vaeyias/one-handed-game-controller/2024_fall/Showcase/FINALHANDLE.SLDPRT

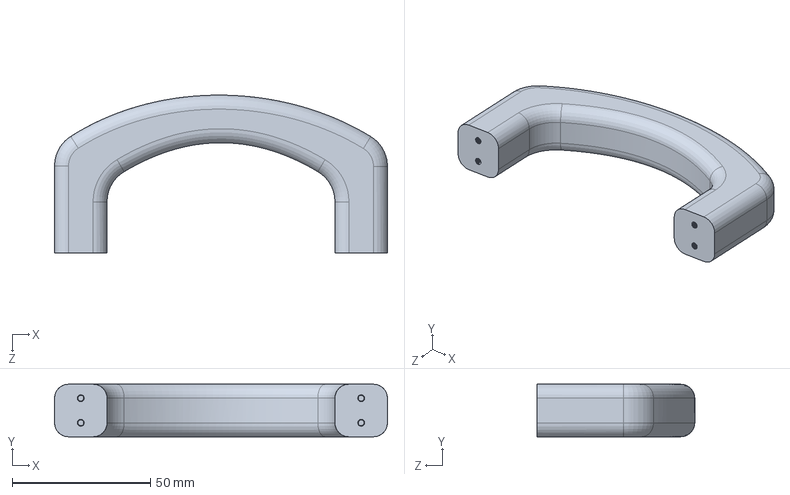
[picture p15: CAD file, 2024-11-24]
2024_fall/Showcase/FINALHANDLE.SLDPRT
120.7 x 19.1 x 57.1 mm
