vaeyias/one-handed-game-controller/2024_spring/solidworks_designs/Button_Updated/playbutton.v6.SLDPRT

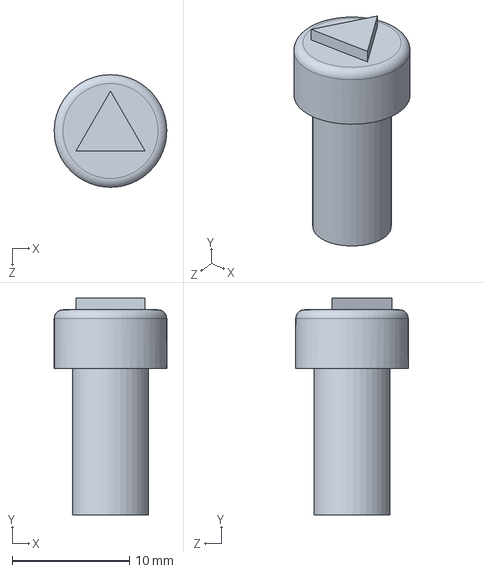
[picture p16: CAD file, 2024-12-06]
2024_spring/solidworks_designs/Button_Updated/playbutton.v6.SLDPRT
9.60 x 18.5 x 9.60 mm
