vaeyias/one-handed-game-controller/2024_spring/solidworks_designs/OHGC_bottom.SLDPRT

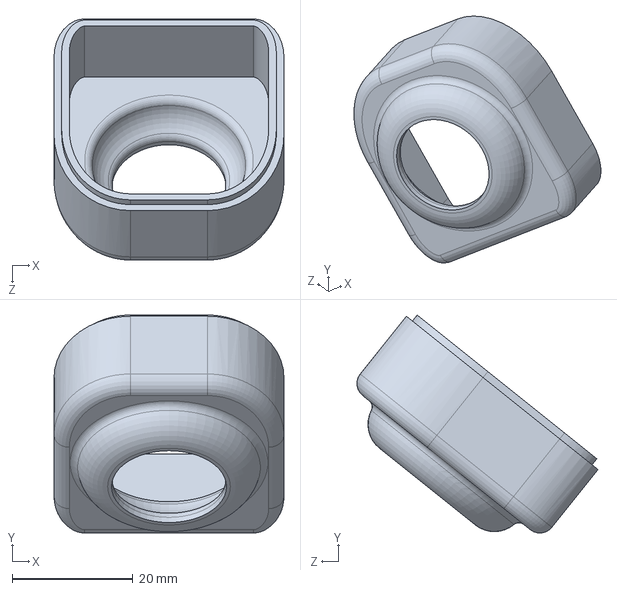
[picture p17: CAD file, 2024-02-22]
2024_spring/solidworks_designs/OHGC_bottom.SLDPRT
38.1 x 36.1 x 39.9 mm
