vaeyias/one-handed-game-controller/2026_spring/SLDPRT-Files/Front_Side.SLDPRT

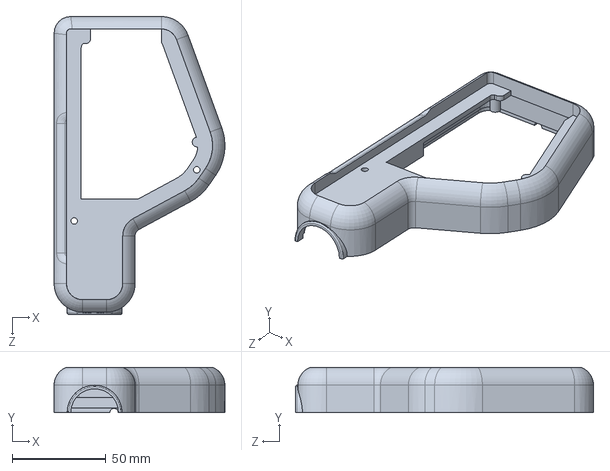
[picture p18: CAD file, 2026-05-03]
2026_spring/SLDPRT-Files/Front_Side.SLDPRT
91.0 x 24.1 x 158.8 mm
