vaeyias/one-handed-game-controller/2024_spring/solidworks_designs/9032.SLDPRT

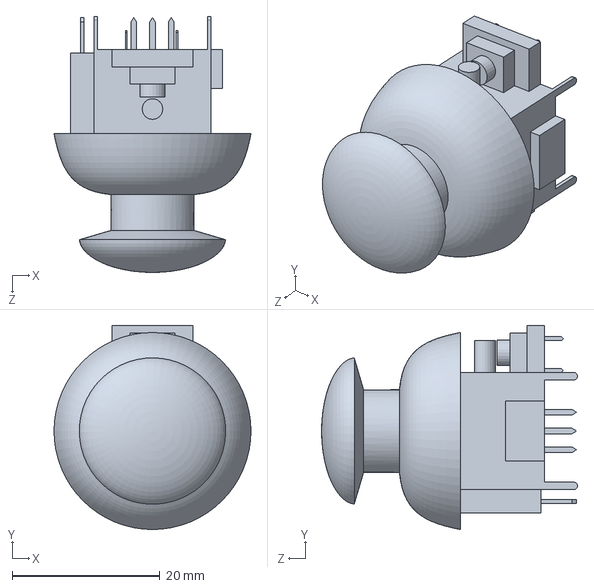
[picture p19: CAD file, 2024-02-22]
2024_spring/solidworks_designs/9032.SLDPRT
26.7 x 27.6 x 34.7 mm
