vaeyias/one-handed-game-controller/2024_spring/solidworks_designs/Button_Updated/triggerbutton.v5.SLDPRT

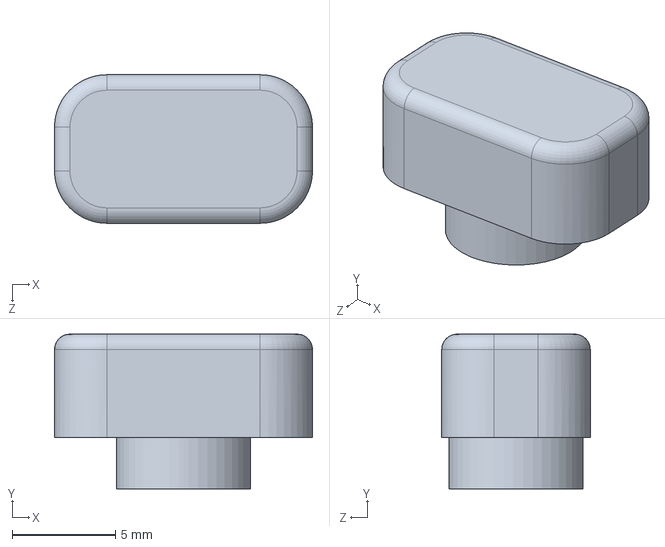
[picture p20: CAD file, 2024-12-06]
2024_spring/solidworks_designs/Button_Updated/triggerbutton.v5.SLDPRT
12.5 x 7.50 x 7.20 mm
