vaeyias/one-handed-game-controller/2026_spring/SLDPRT-Files/B.JoystickMount.SLDPRT

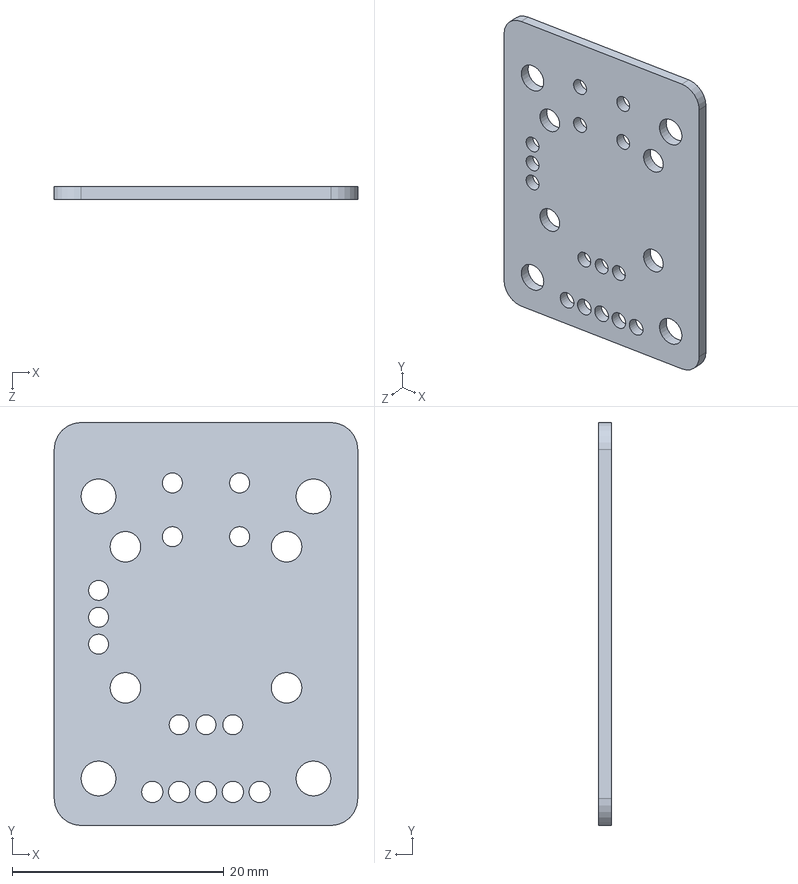
[picture p21: CAD file, 2026-05-01]
2026_spring/SLDPRT-Files/B.JoystickMount.SLDPRT
28.7 x 38.1 x 1.27 mm
