vaeyias/one-handed-game-controller/2024_spring/solidworks_designs/Button_Updated/buttonI.SLDPRT

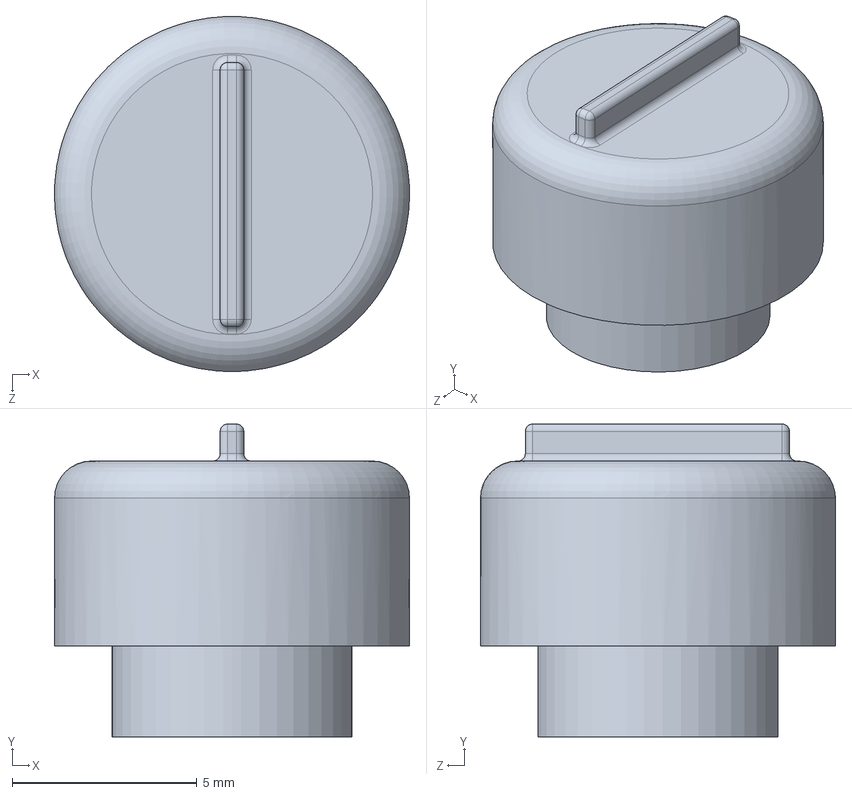
[picture p22: CAD file, 2024-12-06]
2024_spring/solidworks_designs/Button_Updated/buttonI.SLDPRT
9.60 x 8.46 x 9.60 mm
