vaeyias/one-handed-game-controller/2024_spring/solidworks_designs/ButtonType2.SLDPRT

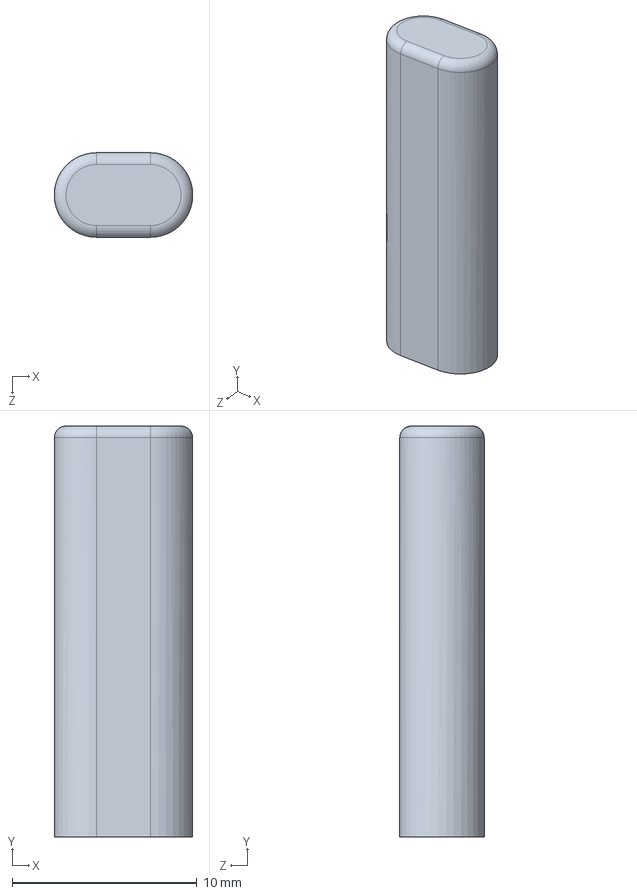
[picture p23: CAD file, 2024-02-22]
2024_spring/solidworks_designs/ButtonType2.SLDPRT
7.48 x 22.2 x 4.57 mm
