vaeyias/one-handed-game-controller/2026_spring/SLDPRT-Files/Back_Side.SLDPRT

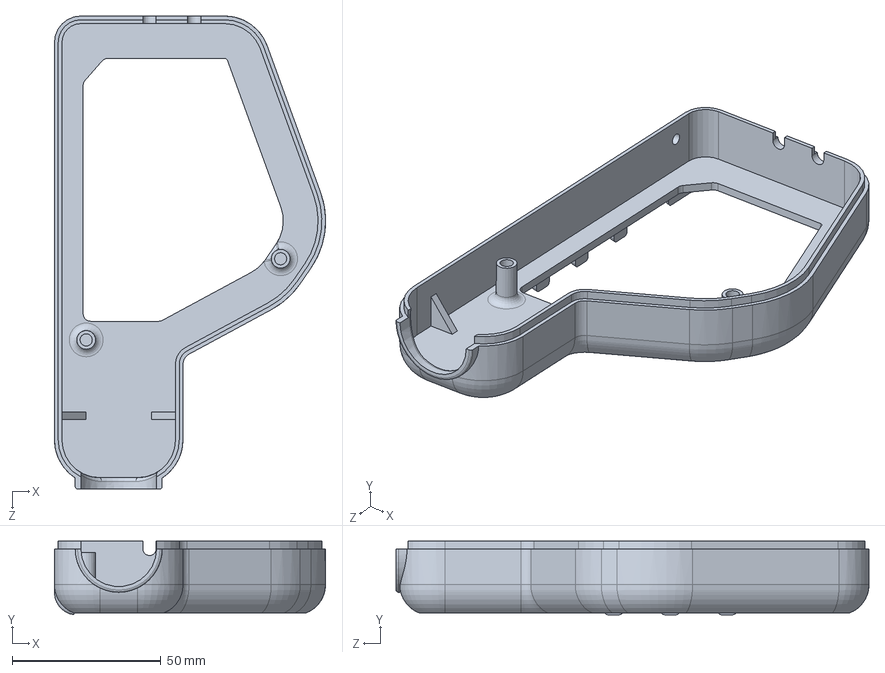
[picture p24: CAD file, 2026-04-27]
2026_spring/SLDPRT-Files/Back_Side.SLDPRT
91.0 x 24.7 x 158.8 mm
