vaeyias/one-handed-game-controller/2024_fall/Showcase/OHGC FRONT_SIDEv2.3.SLDPRT

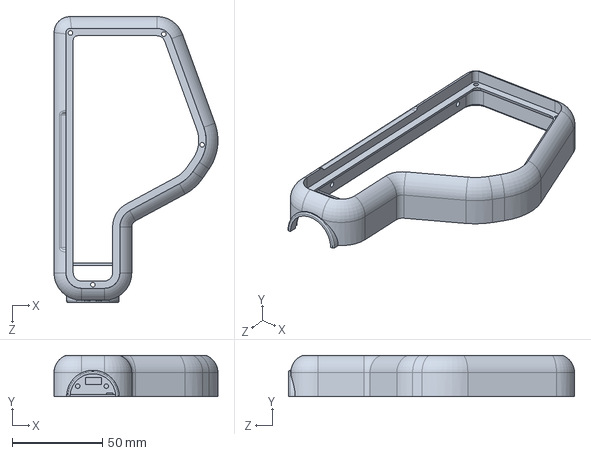
[picture p25: CAD file, 2024-11-17]
2024_fall/Showcase/OHGC FRONT_SIDEv2.3.SLDPRT
91.0 x 22.9 x 158.8 mm
