vaeyias/one-handed-game-controller/2024_spring/solidworks_designs/ButtonTypeDPAD.SLDPRT

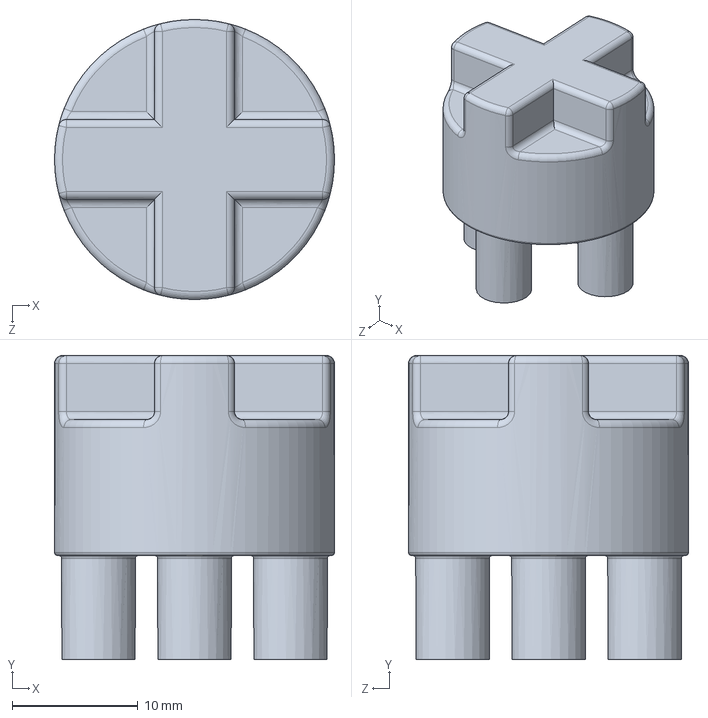
[picture p26: CAD file, 2024-02-22]
2024_spring/solidworks_designs/ButtonTypeDPAD.SLDPRT
22.2 x 24.1 x 22.2 mm
