vaeyias/one-handed-game-controller/2026_spring/SLDPRT-Files/One_Dot_Button.SLDPRT

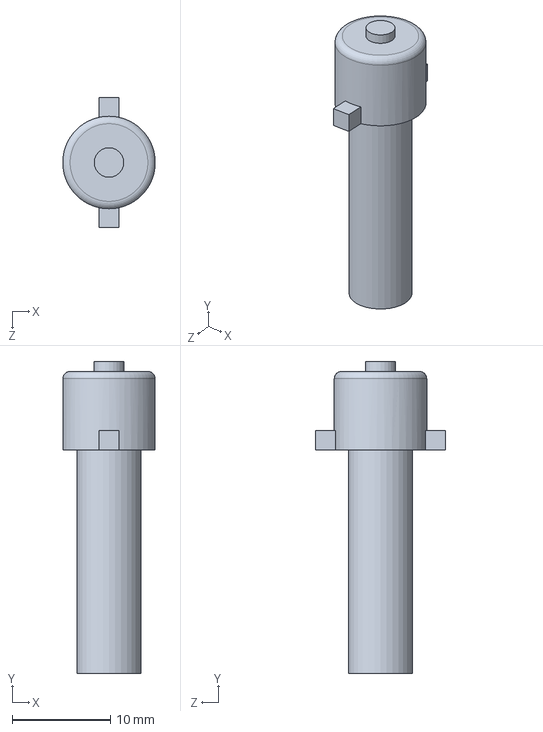
[picture p27: CAD file, 2026-04-23]
2026_spring/SLDPRT-Files/One_Dot_Button.SLDPRT
9.38 x 31.7 x 13.2 mm
