vaeyias/one-handed-game-controller/2024_spring/solidworks_designs/Button_Updated/selectbutton.v4.SLDPRT

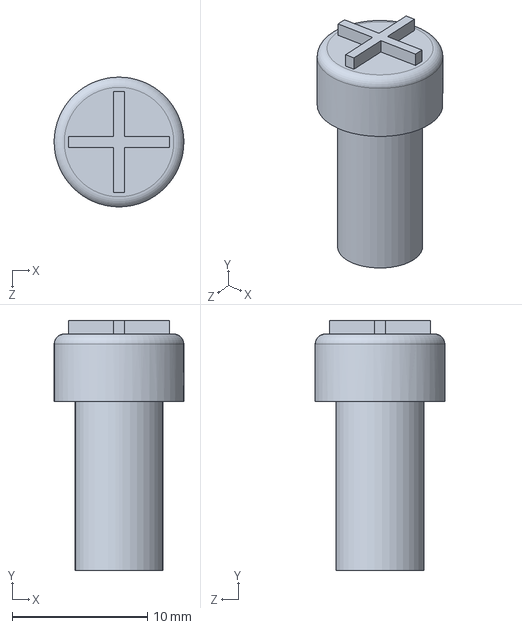
[picture p28: CAD file, 2024-12-06]
2024_spring/solidworks_designs/Button_Updated/selectbutton.v4.SLDPRT
9.60 x 18.5 x 9.60 mm
