vaeyias/one-handed-game-controller/2024_spring/solidworks_designs/OHGC_back_buttonholder.SLDPRT

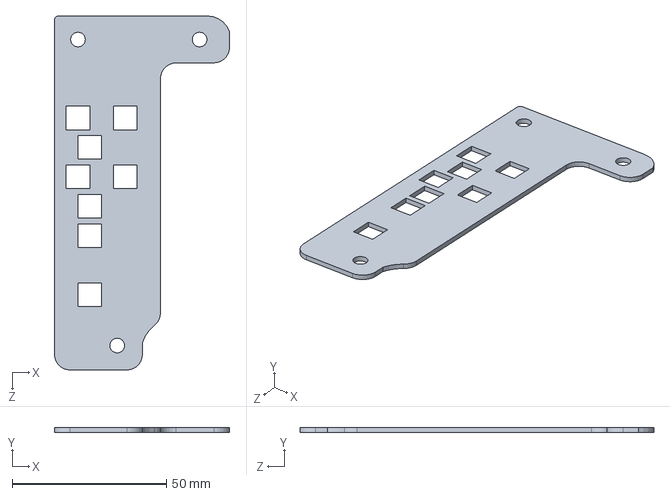
[picture p29: CAD file, 2024-02-22]
2024_spring/solidworks_designs/OHGC_back_buttonholder.SLDPRT
56.7 x 1.59 x 114.6 mm
