vaeyias/one-handed-game-controller/2026_spring/SLDPRT-Files/Blank_Bottom_Button.SLDPRT

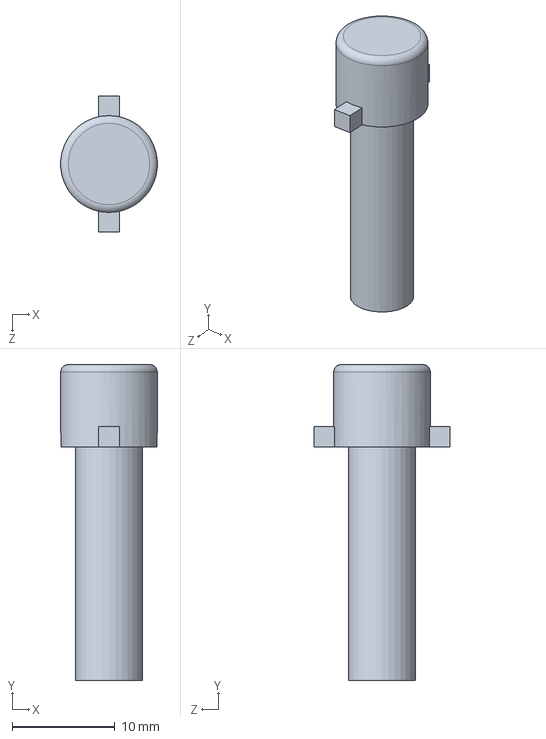
[picture p30: CAD file, 2026-04-23]
2026_spring/SLDPRT-Files/Blank_Bottom_Button.SLDPRT
9.38 x 30.7 x 13.2 mm
