vaeyias/one-handed-game-controller/2024_spring/solidworks_designs/Button_Updated/buttonO.SLDPRT

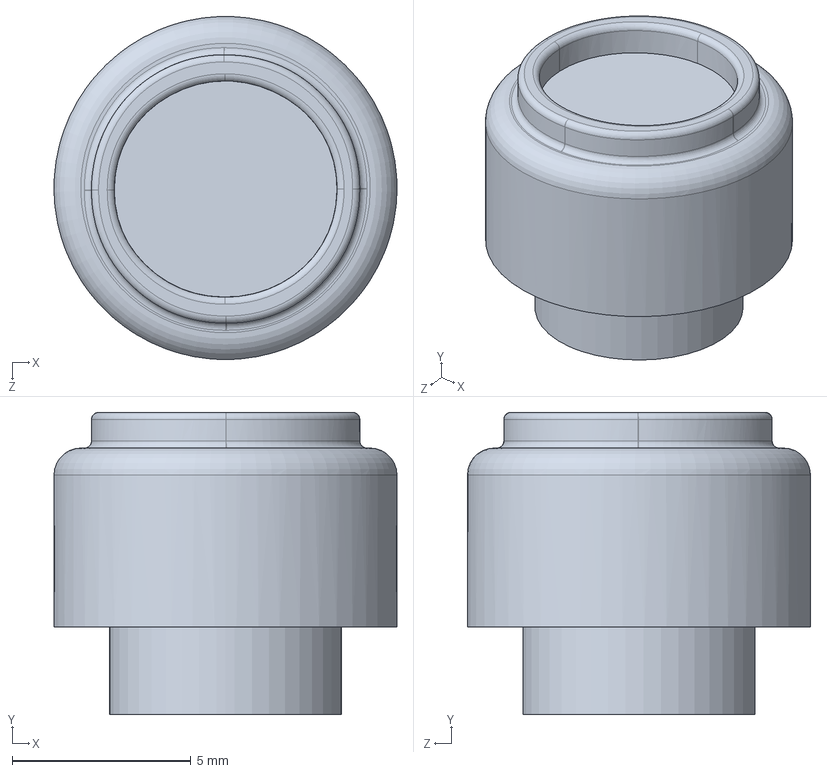
[picture p31: CAD file, 2024-12-06]
2024_spring/solidworks_designs/Button_Updated/buttonO.SLDPRT
9.60 x 8.46 x 9.60 mm
