vaeyias/one-handed-game-controller/2024_spring/solidworks_designs/OHGC_back.SLDPRT

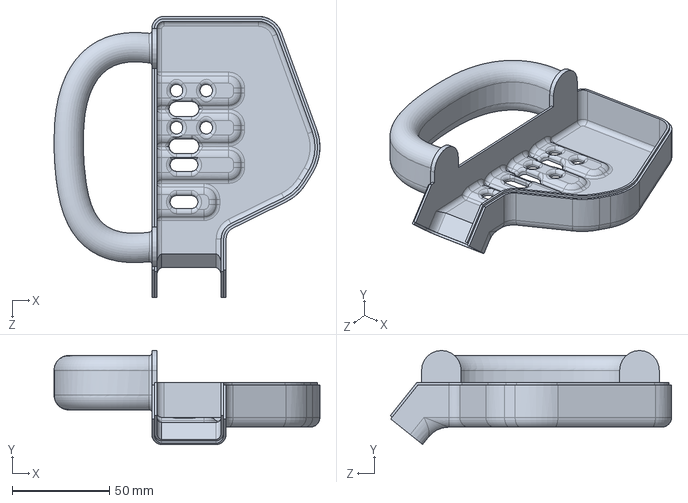
[picture p32: CAD file, 2024-02-22]
2024_spring/solidworks_designs/OHGC_back.SLDPRT
136.4 x 48.2 x 144.3 mm
