vaeyias/one-handed-game-controller/2026_spring/SLDPRT-Files/O_Button.SLDPRT

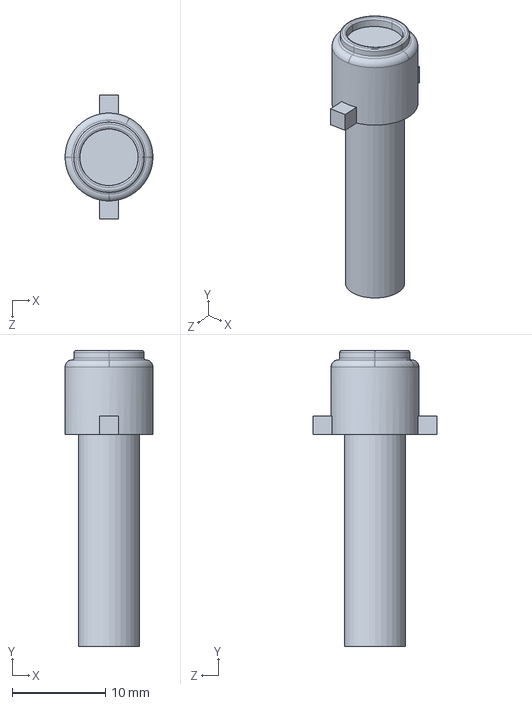
[picture p34: CAD file, 2026-04-23]
2026_spring/SLDPRT-Files/O_Button.SLDPRT
9.40 x 31.7 x 13.2 mm
