vaeyias/one-handed-game-controller/OHGC-Open-Source-Files/OHGC-SLDPRT-Files/Trigger_Button.SLDPRT

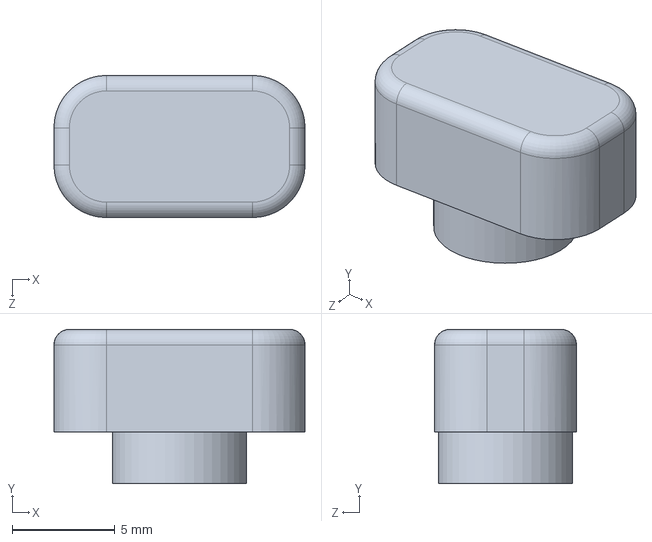
[picture p35: CAD file, 2025-02-03]
OHGC-Open-Source-Files/OHGC-SLDPRT-Files/Trigger_Button.SLDPRT
12.2 x 7.50 x 6.90 mm
