vaeyias/one-handed-game-controller/2024_spring/solidworks_designs/Button_Updated/top_button.v2.4.SLDPRT

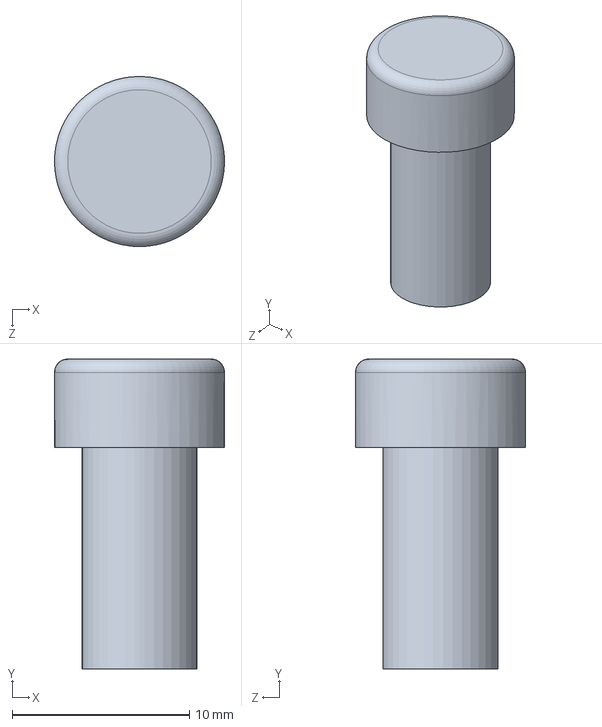
[picture p36: CAD file, 2024-12-06]
2024_spring/solidworks_designs/Button_Updated/top_button.v2.4.SLDPRT
9.60 x 17.5 x 9.60 mm
