vaeyias/one-handed-game-controller/2024_spring/solidworks_designs/ButtonType1.SLDPRT

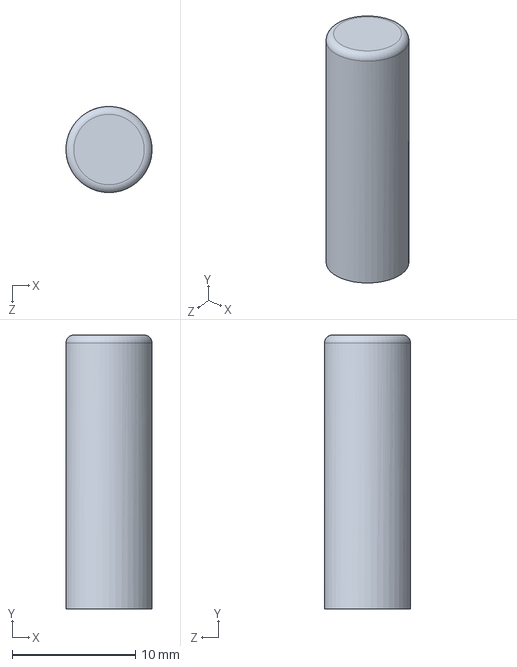
[picture p37: CAD file, 2024-02-22]
2024_spring/solidworks_designs/ButtonType1.SLDPRT
6.98 x 22.2 x 6.98 mm
