vaeyias/one-handed-game-controller/2024_spring/solidworks_designs/ButtonType5.SLDPRT

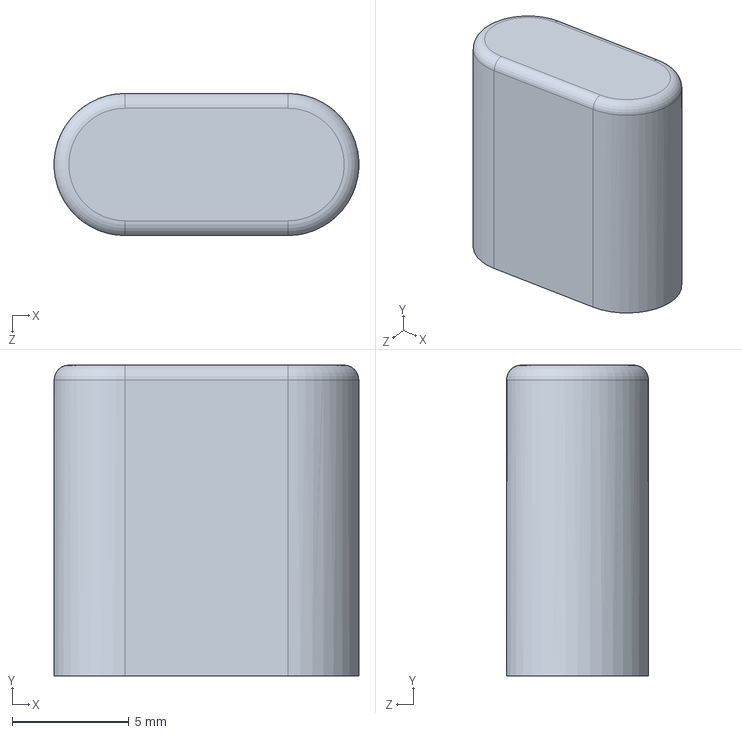
[picture p39: CAD file, 2024-02-22]
2024_spring/solidworks_designs/ButtonType5.SLDPRT
13.1 x 13.3 x 6.10 mm
