vaeyias/one-handed-game-controller/2026_spring/SLDPRT-Files/Bumper_Button.SLDPRT

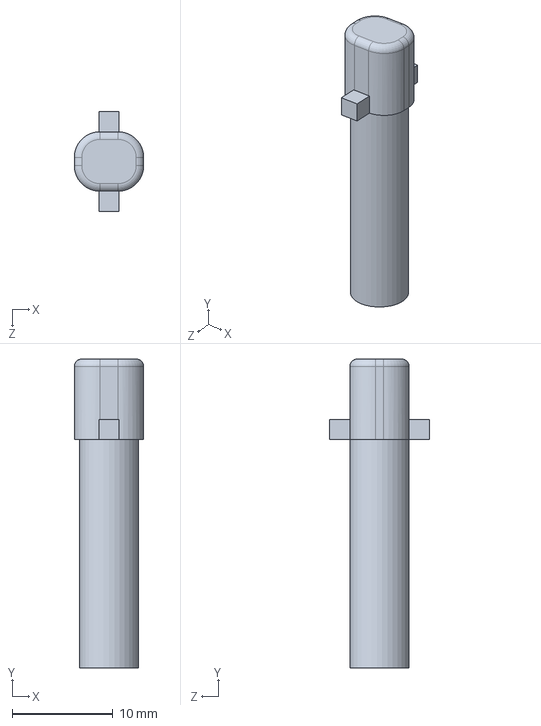
[picture p40: CAD file, 2026-04-23]
2026_spring/SLDPRT-Files/Bumper_Button.SLDPRT
6.90 x 30.7 x 9.96 mm
