vaeyias/one-handed-game-controller/2024_spring/solidworks_designs/OHGC_front_buttonholder.SLDPRT

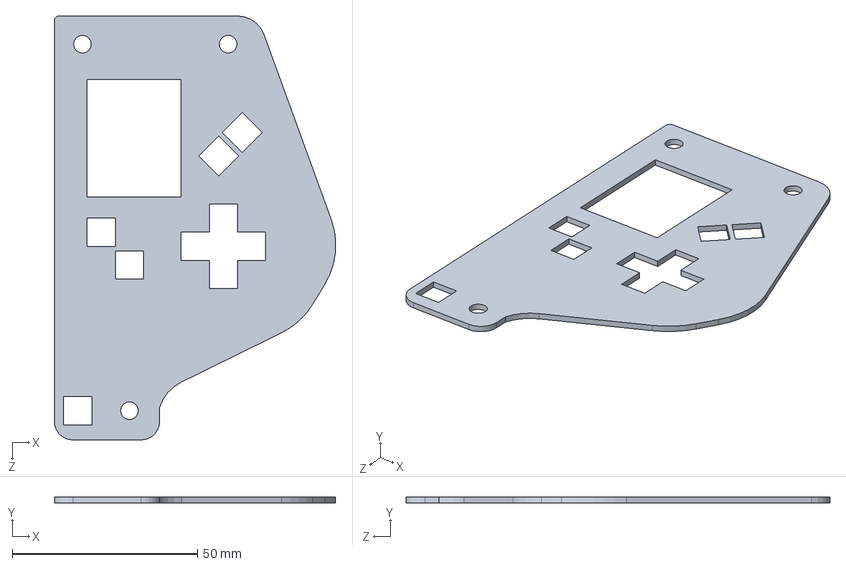
[picture p41: CAD file, 2024-02-22]
2024_spring/solidworks_designs/OHGC_front_buttonholder.SLDPRT
76.1 x 1.59 x 114.6 mm
