vaeyias/one-handed-game-controller/2026_spring/SLDPRT-Files/Trigger_Button.SLDPRT

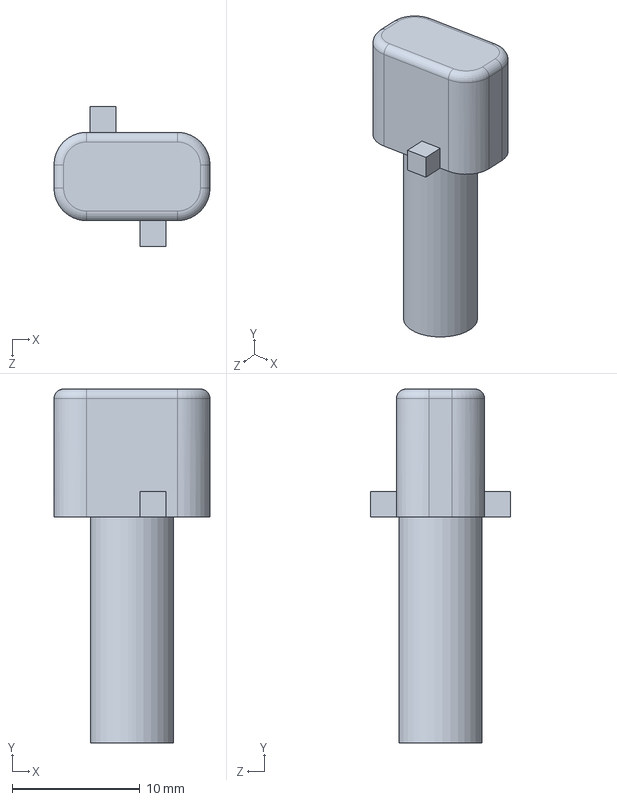
[picture p42: CAD file, 2026-04-23]
2026_spring/SLDPRT-Files/Trigger_Button.SLDPRT
12.2 x 27.7 x 11.0 mm
