vaeyias/one-handed-game-controller/2024_spring/solidworks_designs/ButtonType3.SLDPRT

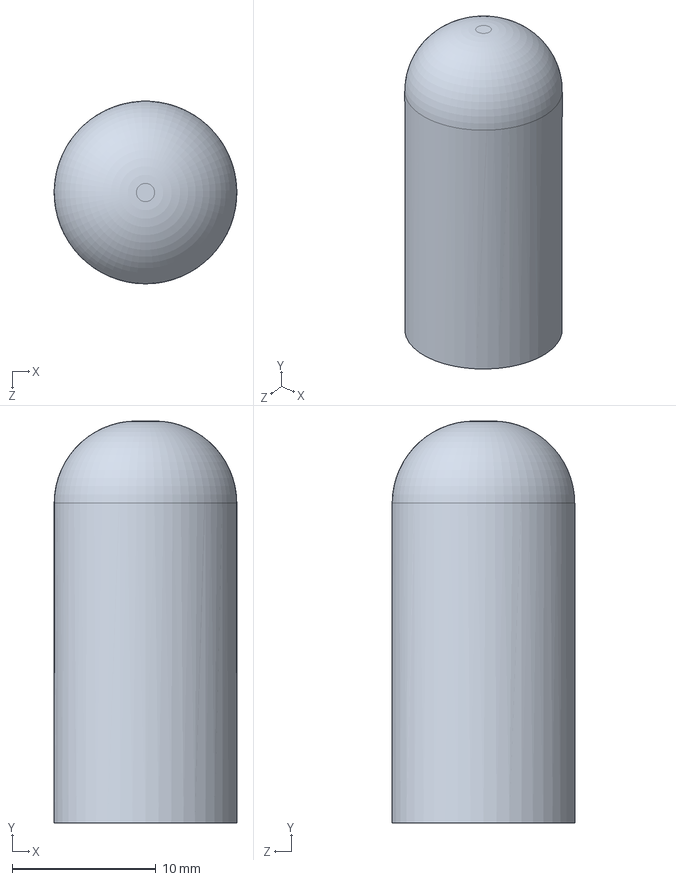
[picture p43: CAD file, 2024-02-22]
2024_spring/solidworks_designs/ButtonType3.SLDPRT
12.7 x 27.9 x 12.7 mm
