vaeyias/one-handed-game-controller/2026_spring/SLDPRT-Files/DPad_Button_Up.SLDPRT

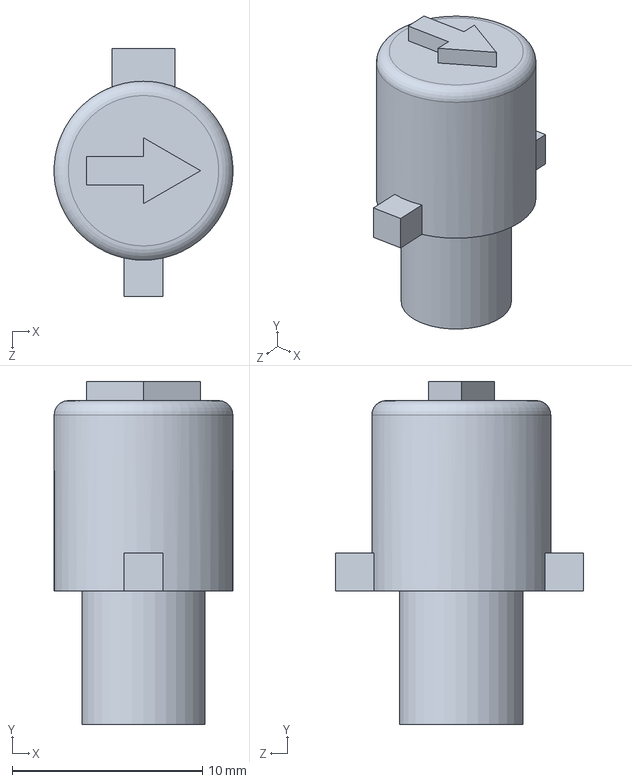
[picture p44: CAD file, 2026-04-17]
2026_spring/SLDPRT-Files/DPad_Button_Up.SLDPRT
9.39 x 18.0 x 13.1 mm
