vaeyias/one-handed-game-controller/2024_spring/solidworks_designs/ButtonType4.SLDPRT

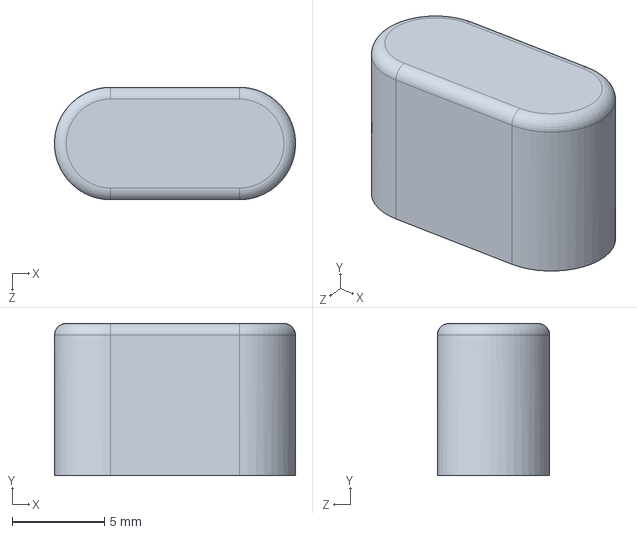
[picture p45: CAD file, 2024-02-22]
2024_spring/solidworks_designs/ButtonType4.SLDPRT
13.1 x 8.26 x 6.10 mm
