vaeyias/one-handed-game-controller/2024_spring/solidworks_designs/OHGC_front.SLDPRT

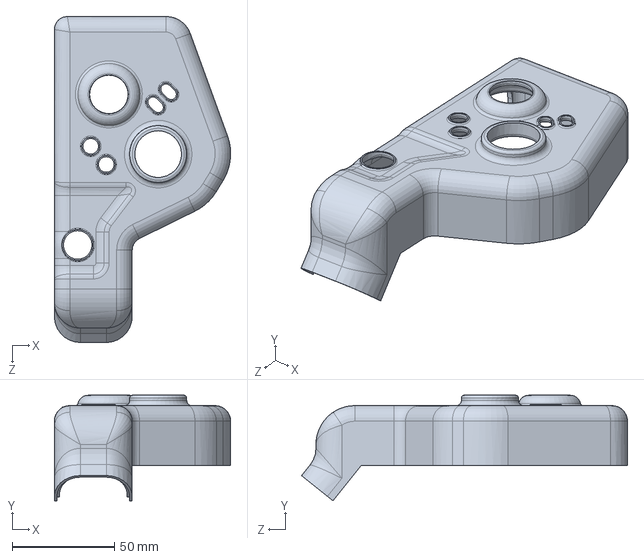
[picture p46: CAD file, 2024-02-22]
2024_spring/solidworks_designs/OHGC_front.SLDPRT
86.3 x 51.6 x 159.5 mm
