vaeyias/one-handed-game-controller/2026_spring/SLDPRT-Files/Select_Button.SLDPRT

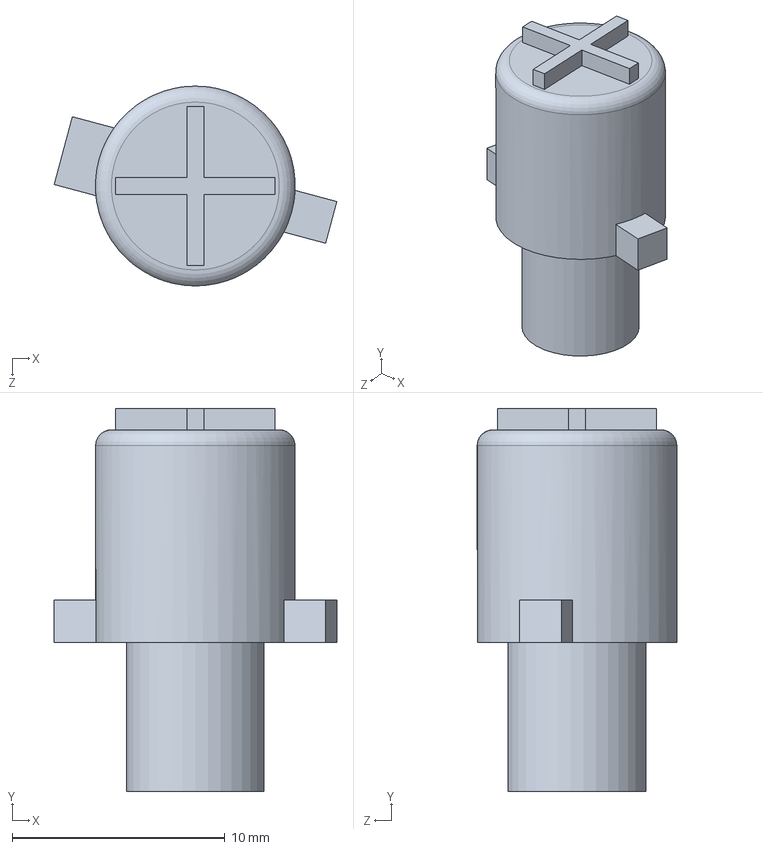
[picture p47: CAD file, 2026-04-17]
2026_spring/SLDPRT-Files/Select_Button.SLDPRT
13.3 x 18.0 x 9.40 mm
