vaeyias/one-handed-game-controller/OHGC-Open-Source-Files/OHGC-SLDPRT-Files/Bumper_Button.SLDPRT

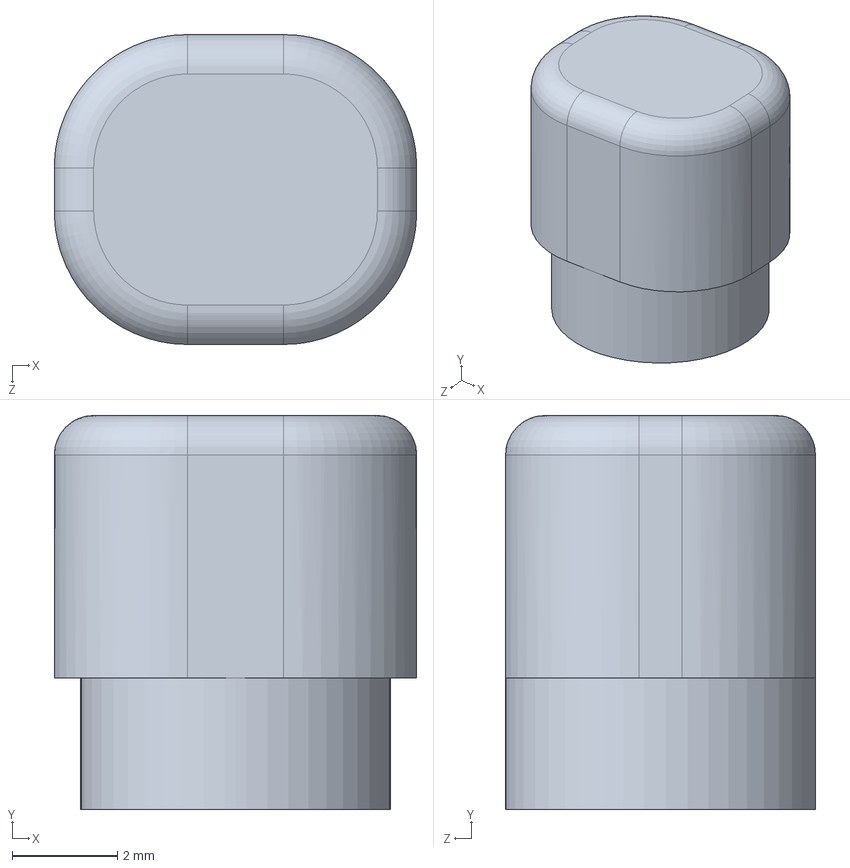
[picture p48: CAD file, 2025-02-03]
OHGC-Open-Source-Files/OHGC-SLDPRT-Files/Bumper_Button.SLDPRT
6.90 x 7.50 x 5.90 mm
