vaeyias/one-handed-game-controller/OHGC-Open-Source-Files/OHGC-SLDPRT-Files/Back_Face.SLDPRT

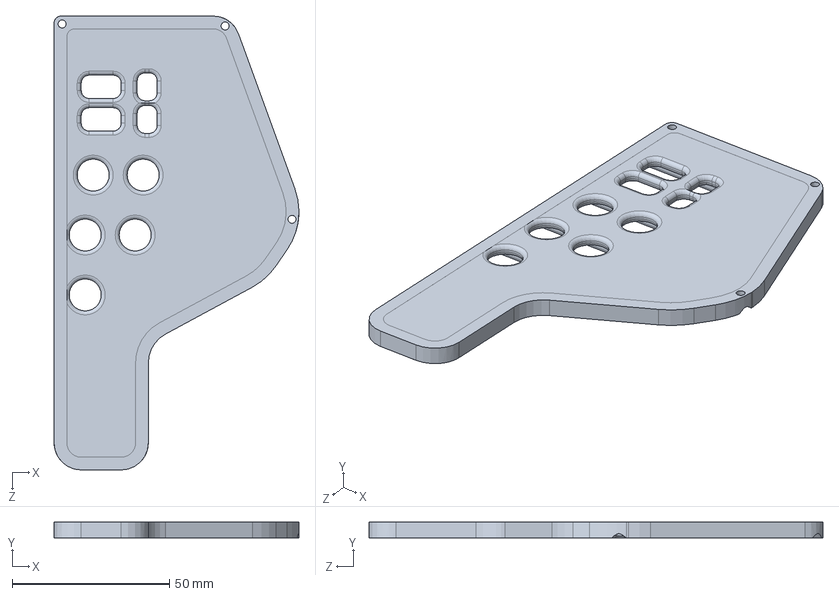
[picture p49: CAD file, 2025-01-15]
OHGC-Open-Source-Files/OHGC-SLDPRT-Files/Back_Face.SLDPRT
77.8 x 5.08 x 144.3 mm
