vaeyias/one-handed-game-controller/2026_spring/SLDPRT-Files/Handle.SLDPRT

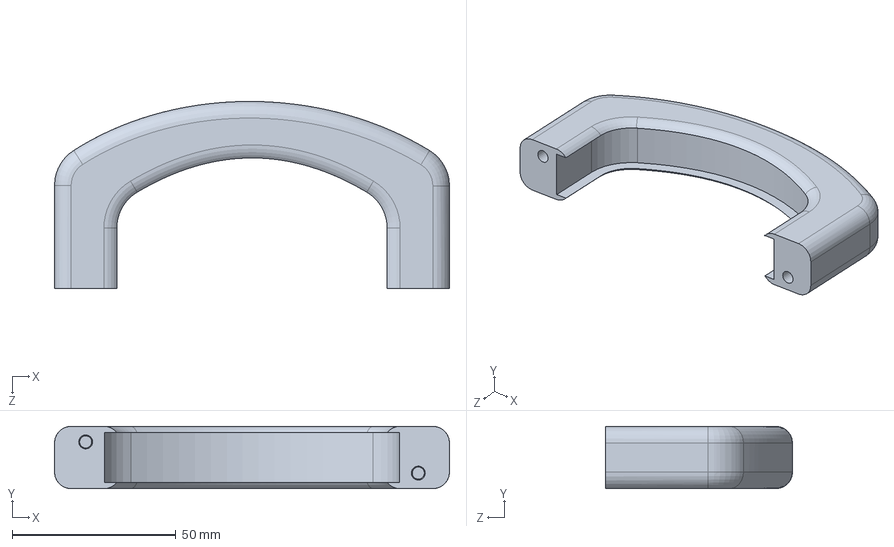
[picture p50: CAD file, 2026-04-07]
2026_spring/SLDPRT-Files/Handle.SLDPRT
120.7 x 19.1 x 57.1 mm
