vaeyias/one-handed-game-controller/OHGC-Open-Source-Files/OHGC-SLDPRT-Files/F_Front_Mount_v4.1.SLDPRT

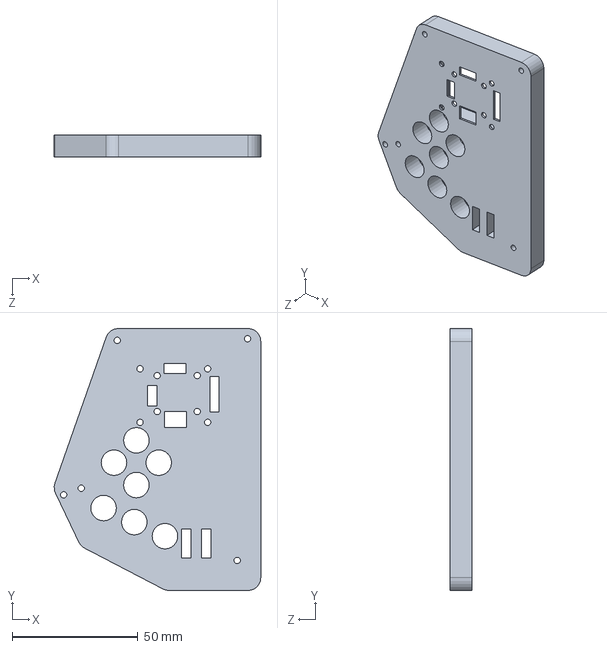
[picture p51: CAD file, 2024-12-25]
OHGC-Open-Source-Files/OHGC-SLDPRT-Files/F_Front_Mount_v4.1.SLDPRT
82.1 x 104.1 x 8.89 mm
