vaeyias/one-handed-game-controller/pcb_designs/updated_sch.kicad_sch

## KiCad design pcb_designs/updated_sch.kicad_sch (2024-03-10)

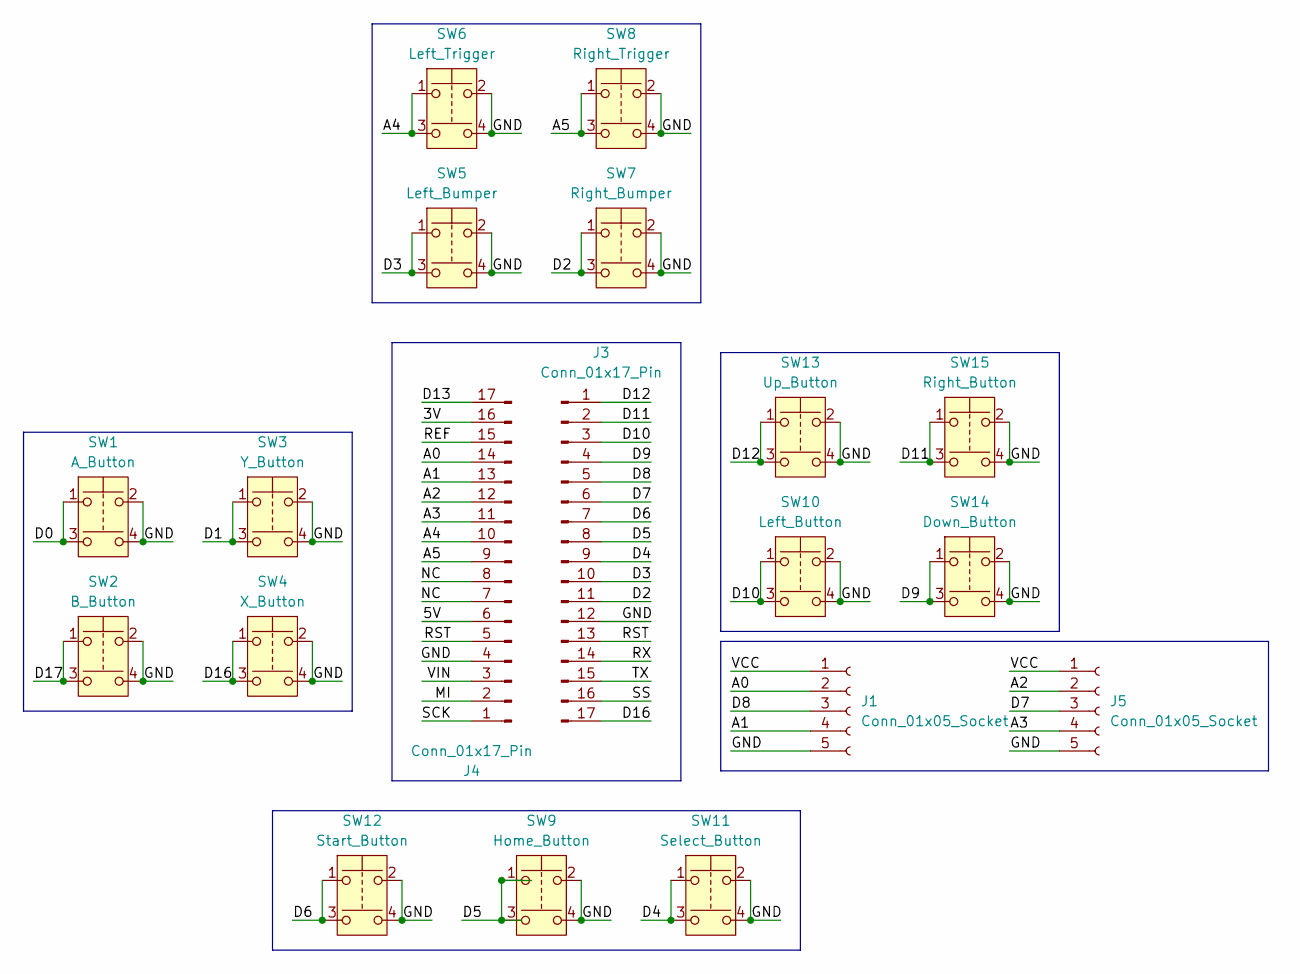
[picture p60: schematic updated_sch.kicad_sch]

Parts:
J1, J5: Conn_01x05_Socket
J3, J4: Conn_01x17_Pin; PinSocket_1x17_P2.54mm_Vertical
SW1: A_Button; Push_E-Switch_KS01Q01
SW2: B_Button; Push_E-Switch_KS01Q01
SW3: Y_Button; Push_E-Switch_KS01Q01
SW4: X_Button; Push_E-Switch_KS01Q01
SW5: Left_Bumper; Push_E-Switch_KS01Q01
SW6: Left_Trigger; Push_E-Switch_KS01Q01
SW7: Right_Bumper; Push_E-Switch_KS01Q01
SW8: Right_Trigger; Push_E-Switch_KS01Q01
SW9: Home_Button; Push_E-Switch_KS01Q01
SW10: Left_Button; Push_E-Switch_KS01Q01
SW11: Select_Button; Push_E-Switch_KS01Q01
SW12: Start_Button; Push_E-Switch_KS01Q01
SW13: Up_Button; Push_E-Switch_KS01Q01
SW14: Down_Button; Push_E-Switch_KS01Q01
SW15: Right_Button; Push_E-Switch_KS01Q01

Connections:
3V: J4.16
5V: J4.6
A0: J1.2, J4.14
A1: J1.4, J4.13
A2: J4.12, J5.2
A3: J4.11, J5.4
A4: J4.10, SW6.1, SW6.3
A5: J4.9, SW8.1, SW8.3
D0: SW1.1, SW1.3
D1: SW3.1, SW3.3
D2: J3.11, SW7.1, SW7.3
D3: J3.10, SW5.1, SW5.3
D4: J3.9, SW11.1, SW11.3
D5: J3.8, SW9.1, SW9.3
D6: J3.7, SW12.1, SW12.3
D7: J3.6, J5.3
D8: J1.3, J3.5
D9: J3.4, SW14.1, SW14.3
D10: J3.3, SW10.1, SW10.3
D11: J3.2, SW15.1, SW15.3
D12: J3.1, SW13.1, SW13.3
D13: J4.17
D16: J3.17, SW4.1, SW4.3
D17: SW2.1, SW2.3
GND: J1.5, J3.12, J4.4, J5.5, SW1.2, SW1.4, SW2.2, SW2.4, SW3.2, SW3.4, SW4.2, SW4.4, SW5.2, SW5.4, SW6.2, SW6.4, SW7.2, SW7.4, SW8.2, SW8.4, SW9.2, SW9.4, SW10.2, SW10.4, SW11.2, SW11.4, SW12.2, SW12.4, SW13.2, SW13.4, SW14.2, SW14.4, SW15.2, SW15.4
MI: J4.2
NC: J4.7, J4.8
REF: J4.15
RST: J3.13, J4.5
RX: J3.14
SCK: J4.1
SS: J3.16
TX: J3.15
VCC: J1.1, J5.1
VIN: J4.3
